hxelec/antc3/logo.h

#define logoWidth  40  // logo width
#define logoHeight 40  // logo height

PROGMEM const unsigned char logo[] = {
   0x00, 0x00, 0x00, 0x00, 0x00, 0x00, 0x00, 0x00, 0x00, 0x00, 0x00, 0x00,
   0x00, 0x00, 0x00, 0x00, 0x00, 0x00, 0x00, 0x00, 0x00, 0x00, 0x00, 0x00,
   0x00, 0xfc, 0xff, 0xff, 0xff, 0x3f, 0xfc, 0xff, 0xff, 0xff, 0x3f, 0xfc,
   0xff, 0xff, 0xff, 0x3f, 0xfc, 0xff, 0xff, 0xff, 0x3f, 0xfc, 0xff, 0xff,
   0xff, 0x3f, 0xfc, 0xff, 0xff, 0xff, 0x3f, 0xfc, 0xff, 0xff, 0xff, 0x3f,
   0xfc, 0xff, 0xff, 0xff, 0x3f, 0x00, 0x00, 0xff, 0x00, 0x00, 0x00, 0x00,
   0xff, 0x00, 0x00, 0x00, 0x00, 0xff, 0x00, 0x00, 0x00, 0x00, 0xff, 0x00,
   0x00, 0x80, 0x1f, 0xff, 0xf8, 0x01, 0x80, 0x1f, 0xff, 0xf8, 0x01, 0x80,
   0x1f, 0xff, 0xf8, 0x01, 0x80, 0x1f, 0xff, 0xf8, 0x01, 0x80, 0x1f, 0xff,
   0xf8, 0x01, 0x80, 0x1f, 0xff, 0xf8, 0x01, 0x00, 0x00, 0xff, 0x00, 0x00,
   0x00, 0x00, 0xff, 0x00, 0x00, 0x00, 0x00, 0xff, 0x00, 0x00, 0x00, 0x00,
   0xff, 0x00, 0x00, 0xfc, 0xff, 0xff, 0xff, 0x3f, 0xfc, 0xff, 0xff, 0xff,
   0x3f, 0xfc, 0xff, 0xff, 0xff, 0x3f, 0xfc, 0xff, 0xff, 0xff, 0x3f, 0xfc,
   0xff, 0xff, 0xff, 0x3f, 0xfc, 0xff, 0xff, 0xff, 0x3f, 0xfc, 0xff, 0xff,
   0xff, 0x3f, 0xfc, 0xff, 0xff, 0xff, 0x3f, 0x00, 0x00, 0x00, 0x00, 0x00,
   0x00, 0x00, 0x00, 0x00, 0x00, 0x00, 0x00, 0x00, 0x00, 0x00, 0x00, 0x00,
   0x00, 0x00, 0x00, 0x00, 0x00, 0x00, 0x00, 0x00 };
